BoujeeEnjinia1701/waterwatch/cad/drawings/WWT-DWG-001.pdf

CONCEPT, NOT FOR FABRICATION | WaterWatch · github.com/BoujeeEnjinia1701/waterwatch

FRONT VIEW
Scale 1:25; looking at the front (along +Y)

TOP VIEW
Scale 1:25; looking down (along -Z)

RIGHT VIEW
Scale 1:25; looking at the right side (along -X)

644

491 2815

GROUND

500 tee

813 cell underside

1300 enclosure center

2,216 overall above ground

260

600 embed

470 riser to pole

300

STATUS LIGHT

EXISTING RISER (NOT IN BOM)

DRAIN TO BASIN

AIR-BREAK VENT

POLE AXIS 103 BEHIND ENCLOSURE CENTER

120

PANEL TILT 30 DEG

ISOMETRIC VIEW
Not to scale; seen from the front right and above, about 30 deg elevation

MAIN DIMENSIONS AND INTERFACES (MM)
Pole 48.3 x 3.2 galvanized, 2100 above ground, 600 in a 300 footing
Panel 5 W, 250 x 190, tilt 30 deg; top 2,216 above ground
Enclosure IP66 200 x 120 x 260, center 1300; sun shield, 25 gap
Status light: 5 mm LED behind a lens in the shield front slot; lead to its own gland Back plates 3 mm aluminium on M8 U-bolts and V-saddles (DDR-003)
Flow cell body 96 x 60 x 74 + 10 lid; cavity 80 x 38 x 66
Cell water 0.19 L; inlet at the bottom, outlet 62 above the underside
Spare pH probe port (M20 gland) in cell lid, plugged (DDR-002)
Tee on the 25 mm riser at 500; valve under the cell; 1/4 in tube 696 Flush 0.5 L/min (pressure compensating) for 90 s hourly (WWT-CAL-001) Drain 12 mm bore with open air break; discharges to the basin Third-angle; front view from -Y, facing the equator; riser on the Z axis
REV | DESCRIPTION | DATE | BY
P1 | Preliminary GA for TRL 3 (from cad/src/model.py) | 2026-09-25 | AC
P2 | Plugged pH probe port in cell lid (DDR-002) | 2026-09-25 | AC
P3 | Layout and labels tidied | 2026-09-25 | AC
P4 | Constructable design: back plates, U-bolts, entries underneath (DDR-003) | 2026-10-02 | AC
P5 | Status light in the shield front, lead to its own gland | 2026-10-02 | AC
WATERWATCH | github.com/BoujeeEnjinia1701/waterwatch

## General arrangement

DRAWING NO.
WWT-DWG-001

REV
P5

SHEET
1 of 1

SIZE

## ANSI B

SCALE
1:25

UNITS
mm
PROJECTION | DATE
2026-10-02

DRAWN
Amish Chadha

MATERIAL / NOTES
Galvanized steel pole; bought-in parts per bom/bom.csv. PRELIMINARY, NOT FOR FABRICATION
Licensed CERN-OHL-S-2.0 · Design Molecule Lab · designmolecule.com | Generated from cad/src; do not edit by hand
