BoujeeEnjinia1701/waterwatch/cad/drawings/WWT-DWG-102.pdf

BUILD PLAN SKETCH, PLAN NOT YET BUILT WaterWatch · github.com/BoujeeEnjinia1701/waterwatch

FRONT VIEW
Scale 1:5; looking at the front (along +Y)

TOP VIEW
Scale 1:5; looking down (along -Z)

RIGHT VIEW
Scale 1:5; looking at the right side (along -X)

200

108 260

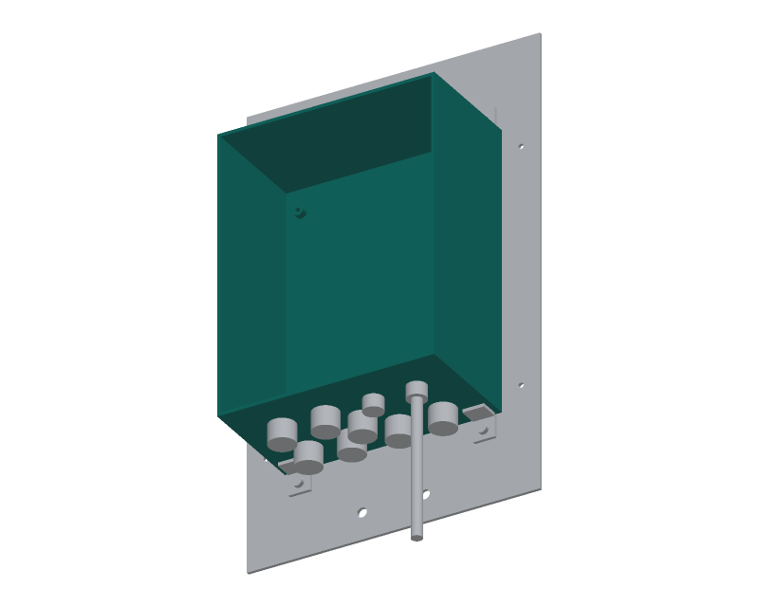
[picture p8: figure]

WHERE IT GOES
This part in colour, its neighbours in grey

HOW TO MAKE IT AND HOW IT FITS
Drawn upside down: stand the box on its top, back face toward you; the top view then shows the bottom face as you see it on the bench. Measure from the back face, and sideways from the centre line
(left and right as seen from the front). See the drilling layout.
Back row, 28 from the back face: valve gland 62 left, chlorine gland 22 left, spare (plugged) 22 right, temperature gland 62 right: 16.2 mm. Front row, 70 from the back face: panel gland 62 left, optics gland
22 left (16.2 mm); vent 22 right (12.2 mm); antenna 62 right (6.5 mm). Middle row, 49 from the back face: status light lead gland on the centre line (16.2 mm).
Tape the face, pilot drill 3 mm slowly with wood behind, open out with a step drill, light pressure. No solvents: polycarbonate crazes.
Check each hole size on the part's datasheet before the last step.
Fit the maker's four lugs to the back corners, feet on top and bottom.
REV | DESCRIPTION | DATE | BY
P1 | Making sketch for the prototype build plan | 2026-10-02 | AC
WATERWATCH | github.com/BoujeeEnjinia1701/waterwatch

## WaterWatch enclosure body: drilling sketch

DRAWING NO.
WWT-DWG-102

REV
P1

SHEET
1 of 1

SIZE

## ANSI B

SCALE
1:5

UNITS
mm
PROJECTION | DATE
2026-10-02

DRAWN
Amish Chadha

MATERIAL / NOTES
Bought IP66 polycarbonate box 200 x 120 x 260 mm, four moulded bosses
Licensed CERN-OHL-S-2.0 · Design Molecule Lab · designmolecule.com | Generated from cad/src; do not edit by hand
