BoujeeEnjinia1701/waterwatch/cad/drawings/WWT-DWG-104.pdf

BUILD PLAN SKETCH, PLAN NOT YET BUILT WaterWatch · github.com/BoujeeEnjinia1701/waterwatch

FRONT VIEW
Scale 1:5; looking at the front (along +Y)

TOP VIEW
Scale 1:5; looking down (along -Z)

RIGHT VIEW
Scale 1:5; looking at the right side (along -X)

254

147 307

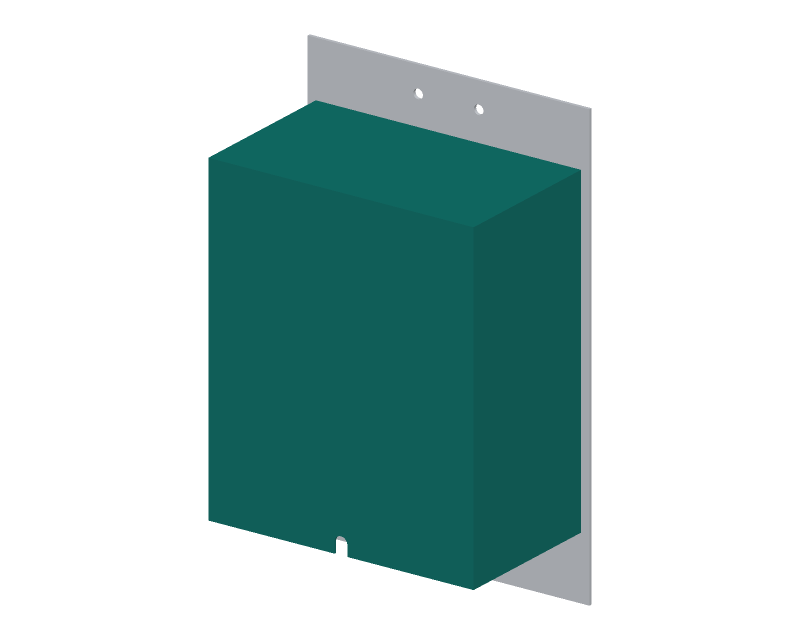
[picture p9: figure]

WHERE IT GOES
This part in colour, its neighbours in grey

HOW TO MAKE IT AND HOW IT FITS
Folded hood 254 wide, 147 deep, 307 tall outside, open at the bottom and the back; 2 mm sheet, bent on a press brake.
Front 254 x 307; two sides 147 deep; top 254 x 147, joined to the sides by folded tabs with two 4 mm rivets each.
Back edge of each side: a 15 mm flange folded 90 degrees inward. Flange holes 5.5 mm, 7.5 in from the side sheet, 40 and 260 up from the lower edge.
Powder coat white after folding; deburr every edge first.
Fit: flanges flat on the back plate, 10 clear of the box; four M5 thumb screws. 25 mm air gap at the front, sides and top.
Front panel: a 12.2 mm slot open at the bottom edge, its round end 10 mm up from the lower edge, for the status light unit.
To open the lid: pull the status light unit down out of its slot,
undo the four thumb screws, slide the shield forward.
Check: on a trial fit the gap is 25 mm (plus or minus 3) all round.
REV | DESCRIPTION | DATE | BY
P1 | Making sketch for the prototype build plan | 2026-10-02 | AC
WATERWATCH | github.com/BoujeeEnjinia1701/waterwatch

## WaterWatch sun shield: making sketch (to a sheet metal shop)

DRAWING NO.
WWT-DWG-104

REV
P1

SHEET
1 of 1

SIZE

## ANSI B

SCALE
1:5

UNITS
mm
PROJECTION | DATE
2026-10-02

DRAWN
Amish Chadha

MATERIAL / NOTES
White powder-coated aluminium sheet 2 mm
Licensed CERN-OHL-S-2.0 · Design Molecule Lab · designmolecule.com | Generated from cad/src; do not edit by hand
