BoujeeEnjinia1701/waterwatch/cad/drawings/WWT-DWG-101.pdf

BUILD PLAN SKETCH, PLAN NOT YET BUILT WaterWatch · github.com/BoujeeEnjinia1701/waterwatch

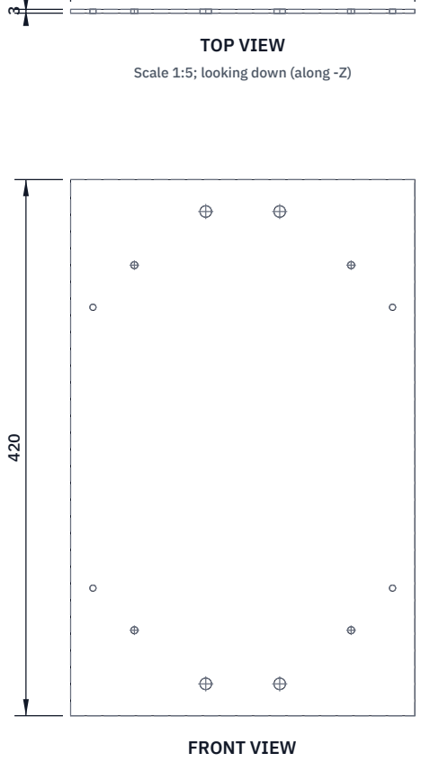
[picture p54: figure]
FRONT VIEW; TOP VIEW; Scale 1:5; looking down (along -Z)

Scale 1:5; looking at the front (along +Y)

RIGHT VIEW
Scale 1:5; looking at the right side (along -X)

270

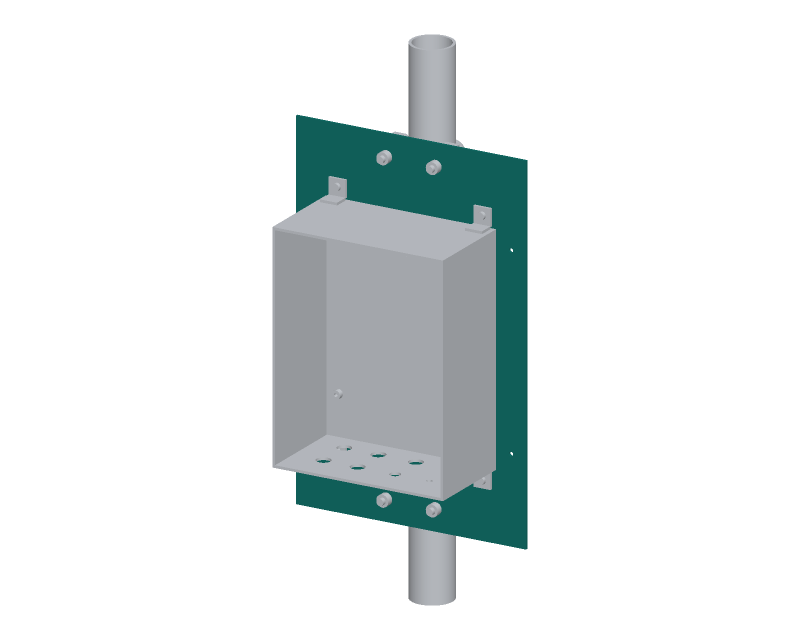
[picture p55: figure]

WHERE IT GOES
This part in colour, its neighbours in grey

HOW TO MAKE IT AND HOW IT FITS
Blank 270 x 420 mm, 3 mm aluminium. Front view: the face the box sits on. Heights from the bottom edge; sideways from the centre line.
U-bolt holes 9 mm at 29 each side, 25 and 395 up (two U-bolts).
Lug screw holes 5.5 mm at 85 each side, 67 and 353 up.
Shield screws: drill 4.2 mm and tap M5 at 117.5 each side,
100 and 320 up (or fit M5 rivet nuts in 7 mm holes).
The box sits centred, from 80 to 340 up; mark its outline. Deburr every hole and edge; round the corners to about 3 mm. Fit: the box's back flat on the front face, held by four lugs;
two V-saddles flat on the back face, one at each U-bolt.
Check: lay the lugs and saddles on it and look through each hole.
REV | DESCRIPTION | DATE | BY
P1 | Making sketch for the prototype build plan | 2026-10-02 | AC
WATERWATCH | github.com/BoujeeEnjinia1701/waterwatch

## WaterWatch enclosure back plate: making sketch

DRAWING NO.
WWT-DWG-101

REV
P1

SHEET
1 of 1

SIZE

## ANSI B

SCALE
1:5

UNITS
mm
PROJECTION | DATE
2026-10-02

DRAWN
Amish Chadha

MATERIAL / NOTES
Aluminium sheet 3 mm, 5052 class, 270 x 420 mm
Licensed CERN-OHL-S-2.0 · Design Molecule Lab · designmolecule.com | Generated from cad/src; do not edit by hand
