BoujeeEnjinia1701/waterwatch/cad/drawings/WWT-DWG-103.pdf

BUILD PLAN SKETCH, PLAN NOT YET BUILT WaterWatch · github.com/BoujeeEnjinia1701/waterwatch

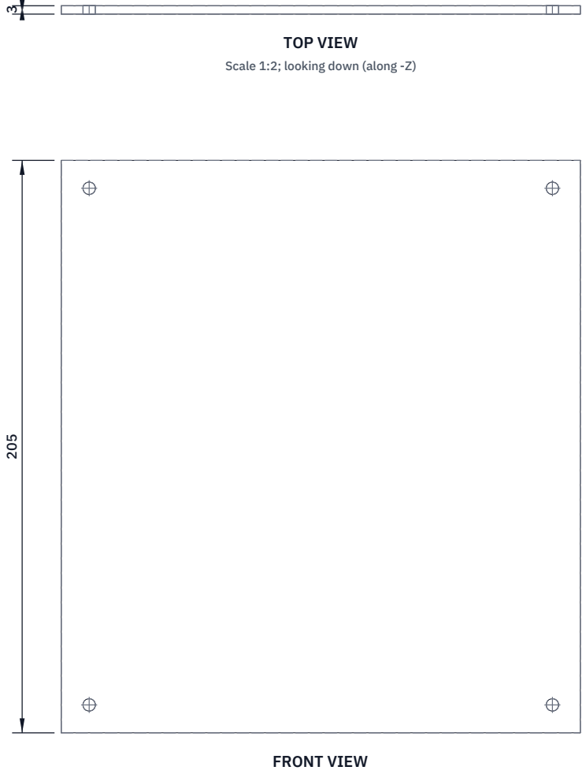
[picture p56: figure]
FRONT VIEW; TOP VIEW; Scale 1:2; looking down (along -Z)

Scale 1:2; looking at the front (along +Y)

RIGHT VIEW
Scale 1:2; looking at the right side (along -X)

186

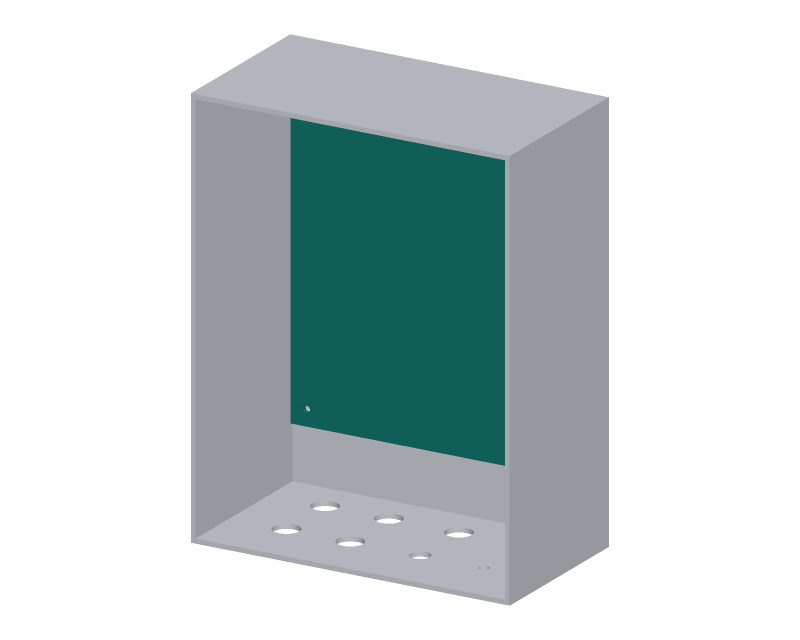
[picture p57: figure]

WHERE IT GOES
This part in colour, its neighbours in grey

HOW TO MAKE IT AND HOW IT FITS
Print flat, 186 wide x 205 tall x 3 mm, ASA, enclosed printer. Four 4.5 mm holes 10 in from each side and from top and bottom (166 x 185 apart) to match the box's four moulded bosses. Measure your box's bosses first and move the holes to suit.
Lay out on the front face, measured from the left and bottom edges: battery 8 to 88 across, 18 to 148 up (strap round it);
modem 18 to 88 across, 150 to 205 up;
controller 93 to 183 across, 45 to 165 up.
Mark each board's holes through the board; drill 3.2 mm for M3 screws on 6 mm nylon standoffs.
Fit: four M4 screws into the bosses; the plate sits 6 off the back wall and 37 above the floor, clear of the gland nuts.
Check: flat within 0.5 mm; drops in and lifts out without force.
REV | DESCRIPTION | DATE | BY
P1 | Making sketch for the prototype build plan | 2026-10-02 | AC
WATERWATCH | github.com/BoujeeEnjinia1701/waterwatch

## WaterWatch internal plate: making sketch

DRAWING NO.
WWT-DWG-103

REV
P1

SHEET
1 of 1

SIZE

## ANSI B

SCALE
1:2

UNITS
mm
PROJECTION | DATE
2026-10-02

DRAWN
Amish Chadha

MATERIAL / NOTES
ASA, 3D printed flat, 100 % infill, 186 x 205 x 3 mm
Licensed CERN-OHL-S-2.0 · Design Molecule Lab · designmolecule.com | Generated from cad/src; do not edit by hand
