BoujeeEnjinia1701/waterwatch/cad/drawings/WWT-DWG-105.pdf

BUILD PLAN SKETCH, PLAN NOT YET BUILT WaterWatch · github.com/BoujeeEnjinia1701/waterwatch

FRONT VIEW
Scale 1:5; looking at the front (along +Y)

TOP VIEW
Scale 1:5; looking down (along -Z)

RIGHT VIEW
Scale 1:5; looking at the right side (along -X)

140

3 385

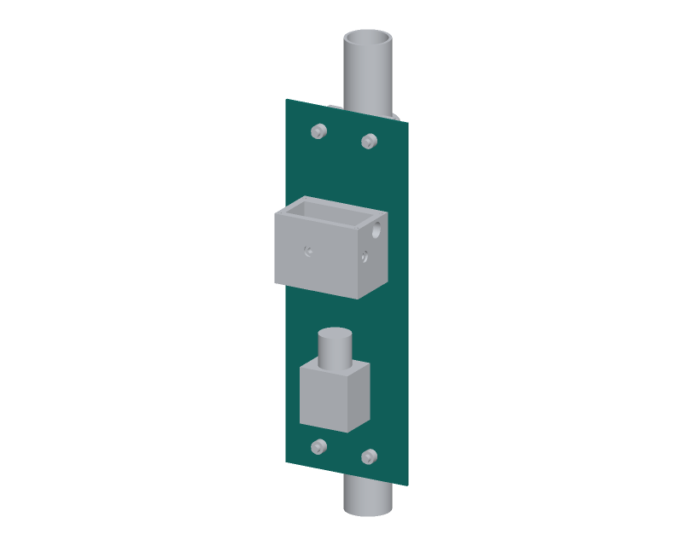
[picture p58: figure]

WHERE IT GOES
This part in colour, its neighbours in grey

HOW TO MAKE IT AND HOW IT FITS
Blank 140 x 385 mm, 3 mm aluminium. Front view: the cell side. Heights from the bottom edge; sideways from the centre line. U-bolt holes 9 mm at 29 each side, 25 and 360 up.
Cell screw holes 5.5 mm at 30 each side, 250 up.
Valve screw holes 4.5 mm at 18 each side, 93 up.
The cell body sits from 213 to 287 up, centred; the valve body from 63 to 123 up, centred, ports level.
Deburr every hole and edge; round the corners to about 3 mm. Fit: cell and valve flat on the front, screws from behind;
two V-saddles flat on the back, one at each U-bolt.
Check: the cell and valve holes line up with their parts.
REV | DESCRIPTION | DATE | BY
P1 | Making sketch for the prototype build plan | 2026-10-02 | AC
WATERWATCH | github.com/BoujeeEnjinia1701/waterwatch

## WaterWatch cell back plate: making sketch

DRAWING NO.
WWT-DWG-105

REV
P1

SHEET
1 of 1

SIZE

## ANSI B

SCALE
1:5

UNITS
mm
PROJECTION | DATE
2026-10-02

DRAWN
Amish Chadha

MATERIAL / NOTES
Aluminium sheet 3 mm, 5052 class, 140 x 385 mm
Licensed CERN-OHL-S-2.0 · Design Molecule Lab · designmolecule.com | Generated from cad/src; do not edit by hand
