BoujeeEnjinia1701/waterwatch/cad/drawings/WWT-DWG-106.pdf

BUILD PLAN SKETCH, PLAN NOT YET BUILT WaterWatch · github.com/BoujeeEnjinia1701/waterwatch

FRONT VIEW
Scale 1:2; looking at the front (along +Y)

TOP VIEW
Scale 1:2; looking down (along -Z)

RIGHT VIEW
Scale 1:2; looking at the right side (along -X)

96

60 74

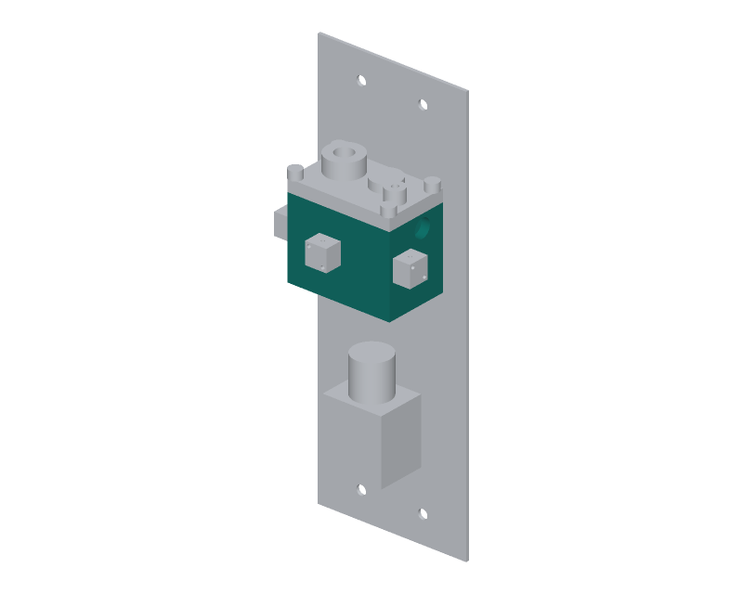
[picture p59: figure]

WHERE IT GOES
This part in colour, its neighbours in grey

HOW TO MAKE IT AND HOW IT FITS
Block 96 wide x 60 deep x 74 tall. Pocket 80 x 38, 66 deep, from the top: walls 8 at the front, left and right, 14 at the back, floor 8.
Baffle 6 x 26 x 40 tall on the back wall, 2 right of centre: leave
it when milling, or solvent-weld a PVC strip.
Windows 6 mm through, 41 up, each with a 12 mm counterbore 2.5 deep outside: left and right walls 14 from the front face; front wall
8 left of centre. Bed a 2 mm acrylic disc in each with silicone.
Inlet: floor, 32 left of centre, 37.5 from the front; tap 1/8 BSPT.
Outlet: right wall, 62 up, 37 from the front; tap 3/8 BSP.
Back face: two M5 holes 12 deep at 30 each side, 37 up.
Top: four M4 holes 12 deep at 44 each side, 4 and 53 from the front. Check: fill with water to the outlet; no leak in 30 min.
REV | DESCRIPTION | DATE | BY
P1 | Making sketch for the prototype build plan | 2026-10-02 | AC
WATERWATCH | github.com/BoujeeEnjinia1701/waterwatch

## WaterWatch flow cell body: making sketch

DRAWING NO.
WWT-DWG-106

REV
P1

SHEET
1 of 1

SIZE

## ANSI B

SCALE
1:2

UNITS
mm
PROJECTION | DATE
2026-10-02

DRAWN
Amish Chadha

MATERIAL / NOTES
Black PVC block (or ASA printed 100 % infill), 96 x 60 x 74 mm
Licensed CERN-OHL-S-2.0 · Design Molecule Lab · designmolecule.com | Generated from cad/src; do not edit by hand
