BoujeeEnjinia1701/waterwatch/cad/drawings/WWT-DWG-107.pdf

BUILD PLAN SKETCH, PLAN NOT YET BUILT WaterWatch · github.com/BoujeeEnjinia1701/waterwatch

FRONT VIEW
Scale 2:1; looking at the front (along +Y)

TOP VIEW
Scale 2:1; looking down (along -Z)

RIGHT VIEW
Scale 2:1; looking at the right side (along -X)

20

16 20

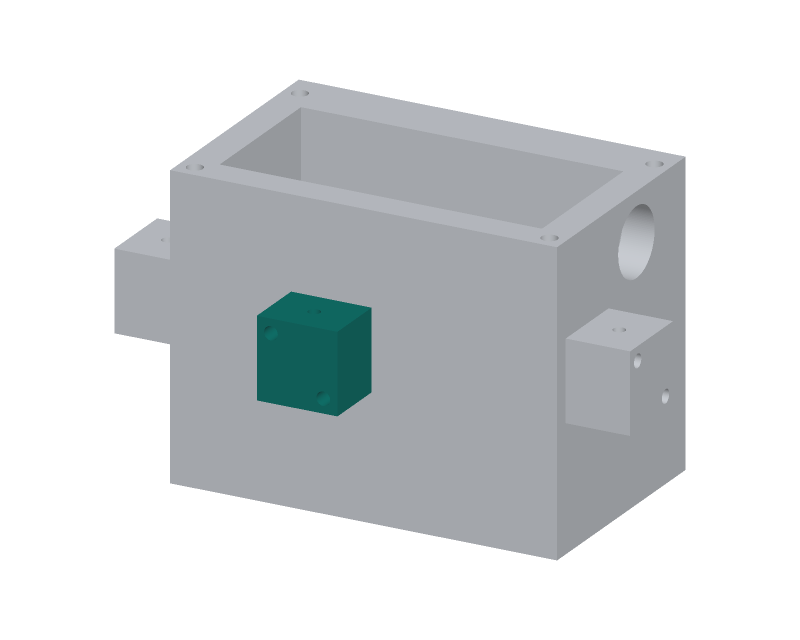
[picture p60: figure]

WHERE IT GOES
This part in colour, its neighbours in grey

HOW TO MAKE IT AND HOW IT FITS
Make three the same, 20 x 20 x 16 mm, in black ASA.
A 5 mm bore on the axis from the wall face, 12 deep, for the LED (left wall) or a light-to-frequency detector (front and right).
A 3 mm hole from the bore out of the top for the leads.
Two 3.4 mm holes at opposite corners, 3.5 in from the edges, for M3 screws into tapped holes beside each window.
Seat the LED or detector against the window disc, pot it in black epoxy so no daylight leaks in, and lead the wires out of the top. Fit: face flat on the cell wall, centred on its window.
Check: in the dark, the detector reads the same with the room light on and off.
REV | DESCRIPTION | DATE | BY
P1 | Making sketch for the prototype build plan | 2026-10-02 | AC
WATERWATCH | github.com/BoujeeEnjinia1701/waterwatch

## WaterWatch optics holder (make 3): making sketch

DRAWING NO.
WWT-DWG-107

REV
P1

SHEET
1 of 1

SIZE

## ANSI B

SCALE
2:1

UNITS
mm
PROJECTION | DATE
2026-10-02

DRAWN
Amish Chadha

MATERIAL / NOTES
Black ASA, 3D printed, 100 % infill, 20 x 20 x 16 mm
Licensed CERN-OHL-S-2.0 · Design Molecule Lab · designmolecule.com | Generated from cad/src; do not edit by hand
