BoujeeEnjinia1701/waterwatch/cad/drawings/WWT-DWG-108.pdf

BUILD PLAN SKETCH, PLAN NOT YET BUILT WaterWatch · github.com/BoujeeEnjinia1701/waterwatch

FRONT VIEW
Scale 1:2; looking at the front (along +Y)

TOP VIEW
Scale 1:2; looking down (along -Z)

RIGHT VIEW
Scale 1:2; looking at the right side (along -X)

16

16 123

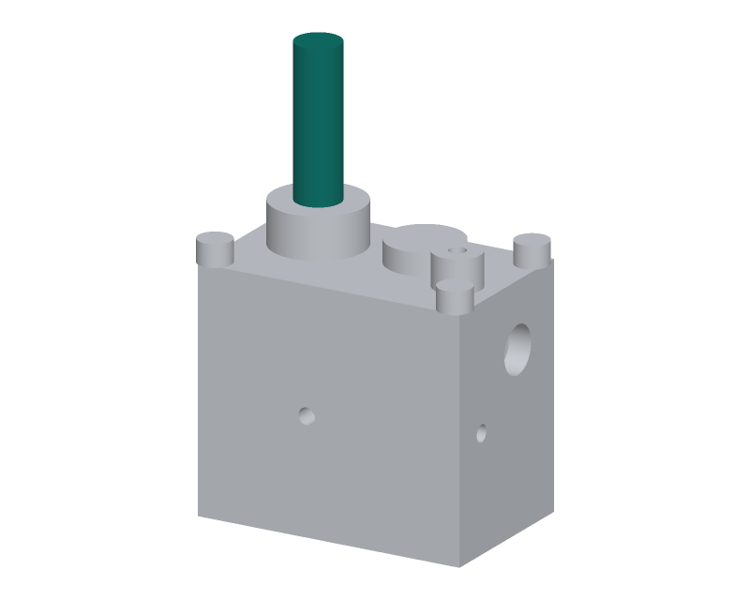
[picture p61: figure]

WHERE IT GOES
This part in colour, its neighbours in grey

HOW TO MAKE IT AND HOW IT FITS
Body: 120 mm of 16 mm PVC conduit. Electrodes on a 9 mm circle, 120 degrees apart, standing 3 mm proud of the tip:
working: 2 mm graphite rod (pencil lead class), polished flat; reference: chlorided silver (Ag/AgCl) wire; counter: stainless wire. Solder each lead to a core of a shielded 3-core cable.
Hold the electrodes in a printed jig and pot the bottom 20 mm of the tube in epoxy; seal the top round the cable with heat shrink.
Wet the tip, sand the graphite face with 1200 grit before use.
Fit: through the M25 gland in the cell lid; tip 40 mm below the
top of the body, clear of the walls and the beam.
Check: electrodes isolated from each other (over 10 megohm dry).
REV | DESCRIPTION | DATE | BY
P1 | Making sketch for the prototype build plan | 2026-10-02 | AC
WATERWATCH | github.com/BoujeeEnjinia1701/waterwatch

## WaterWatch free chlorine sensor: making sketch

DRAWING NO.
WWT-DWG-108

REV
P1

SHEET
1 of 1

SIZE

## ANSI B

SCALE
1:2

UNITS
mm
PROJECTION | DATE
2026-10-02

DRAWN
Amish Chadha

MATERIAL / NOTES
PVC conduit 16 mm OD; graphite rod, Ag/AgCl wire, stainless wire; epoxy
Licensed CERN-OHL-S-2.0 · Design Molecule Lab · designmolecule.com | Generated from cad/src; do not edit by hand
