BoujeeEnjinia1701/waterwatch/cad/drawings/WWT-DWG-109.pdf

BUILD PLAN SKETCH, PLAN NOT YET BUILT WaterWatch · github.com/BoujeeEnjinia1701/waterwatch

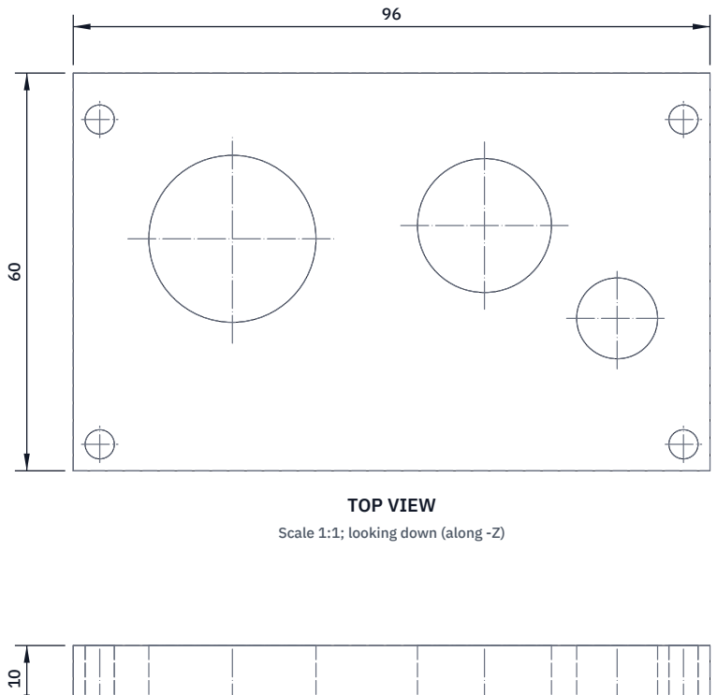
[picture p62: figure]
TOP VIEW; Scale 1:1; looking down (along -Z)

FRONT VIEW
Scale 1:1; looking at the front (along +Y)

RIGHT VIEW
Scale 1:1; looking at the right side (along -X)

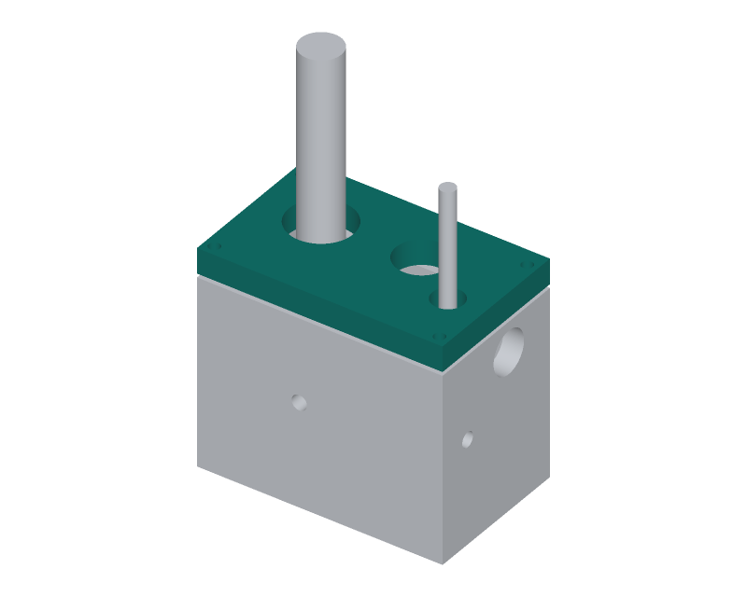
[picture p63: figure]

WHERE IT GOES
This part in colour, its neighbours in grey

HOW TO MAKE IT AND HOW IT FITS
Lid 96 x 60 x 10 mm. Measure from the front edge and the centre line. Chlorine gland: tap M25 x 1.5, 24 left of centre, 35 from the front. Spare pH port: tap M20 x 1.5, 14 right of centre, 37 from the front; fit the blanking plug (or a gland for the pH probe variant).
Temperature gland: tap M12 x 1.5, 34 right, 23 from the front. Stud holes 4.5 mm at 44 each side, 4 and 53 from the front. Gasket: same outline, 80 x 38 window centred 27 from the front, four 4.5 mm stud holes; cut from 1.5 mm EPDM.
Fit: four M4 studs in the body, gasket, lid, four knurled thumb nuts, finger tight. The lid lifts off with the sensors in it.
Check: glands do not touch each other or the thumb nuts.
REV | DESCRIPTION | DATE | BY
P1 | Making sketch for the prototype build plan | 2026-10-02 | AC
WATERWATCH | github.com/BoujeeEnjinia1701/waterwatch

## WaterWatch flow cell lid and gasket: making sketch

DRAWING NO.
WWT-DWG-109

REV
P1

SHEET
1 of 1

SIZE

## ANSI B

SCALE
1:1

UNITS
mm
PROJECTION | DATE
2026-10-02

DRAWN
Amish Chadha

MATERIAL / NOTES
Black PVC sheet 10 mm; EPDM sheet 1.5 mm for the gasket
Licensed CERN-OHL-S-2.0 · Design Molecule Lab · designmolecule.com | Generated from cad/src; do not edit by hand
