BoujeeEnjinia1701/waterwatch/media/card.png

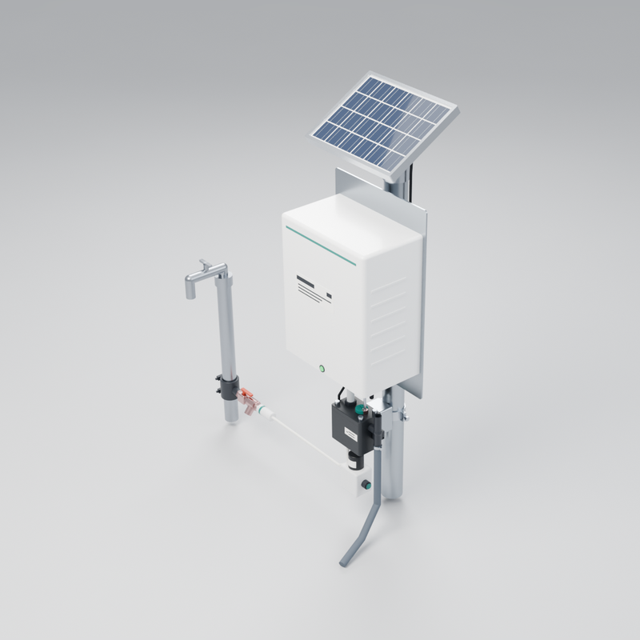
media/card.png
