BoujeeEnjinia1701/waterwatch/media/concept-blueprint.png

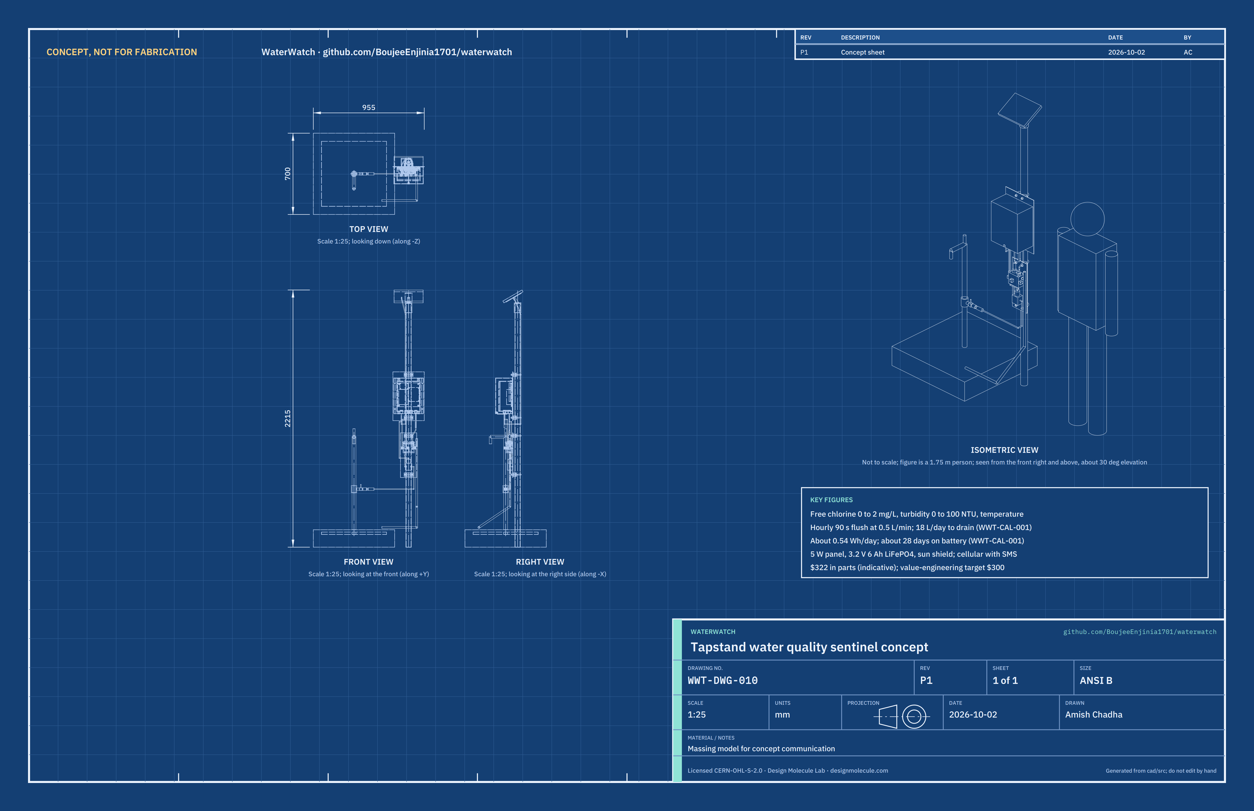
media/concept-blueprint.png
