BoujeeEnjinia1701/waterwatch/media/render-detail.png

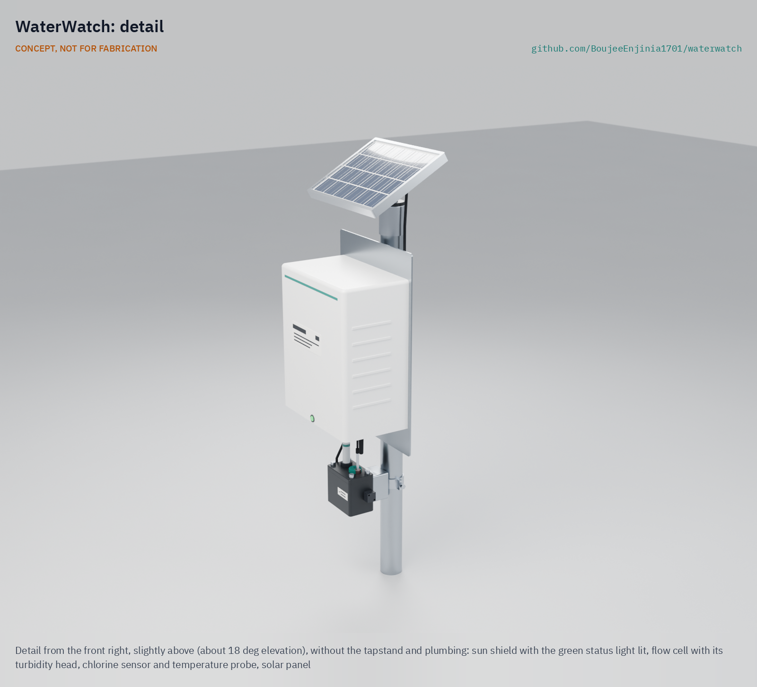
media/render-detail.png
