BoujeeEnjinia1701/waterwatch/media/render-exploded.png

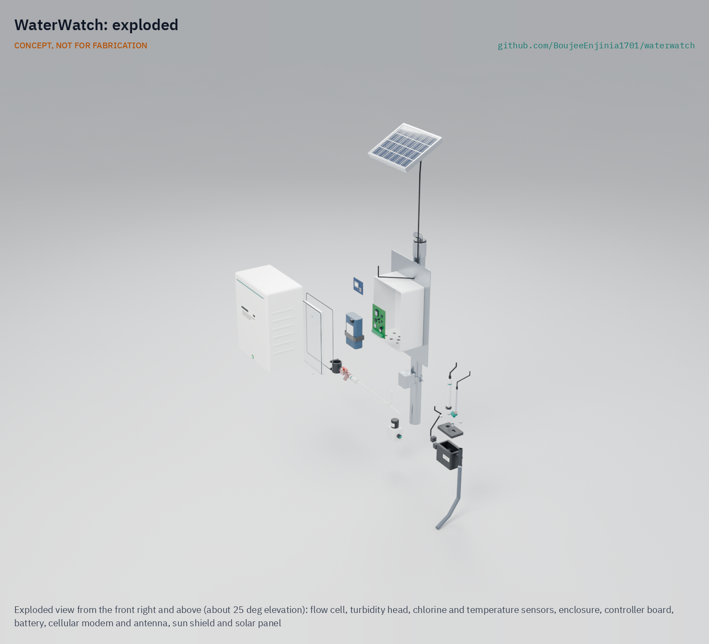
media/render-exploded.png
