BoujeeEnjinia1701/waterwatch/media/social-preview.png

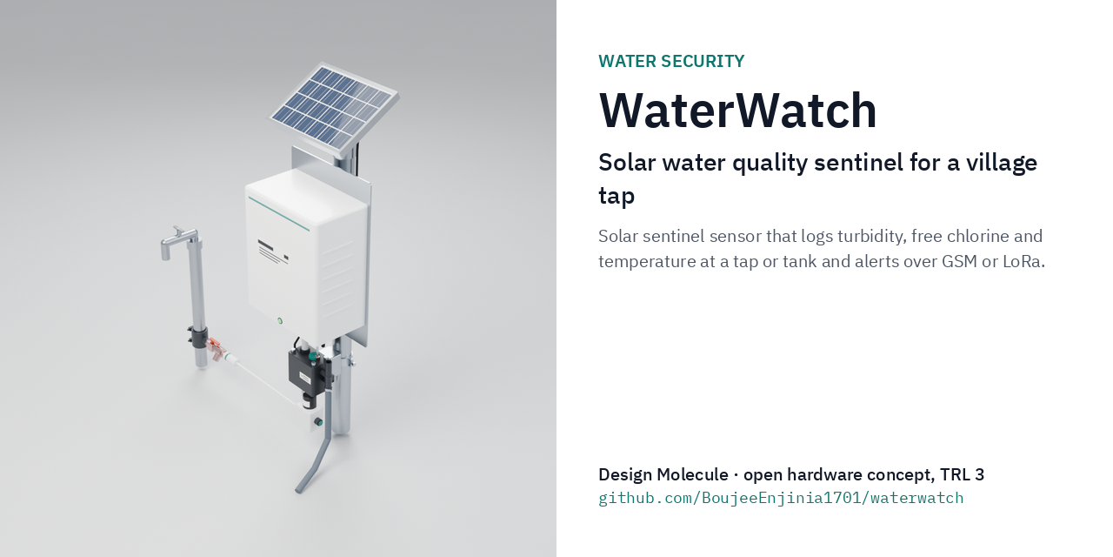
media/social-preview.png
